jmos1/COUNTER_V01/Outputs/Images/bottom.PNG

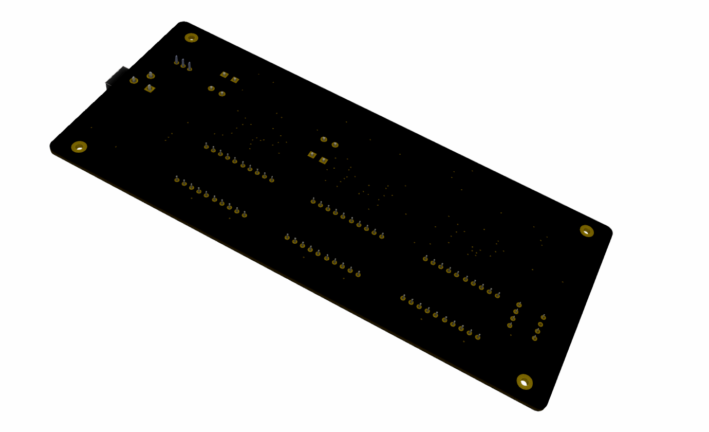
Outputs/Images/bottom.PNG
